tom-biskupic/LabPSU/Firmware/LabPSU/Linearizer.h

/* 
* Linearizer.h
*
* Author: tom
*/

#include <stdint.h>

#ifndef __LINEARIZER_H__
#define __LINEARIZER_H__

/*
The Linearizer is used to linearize the output of a DAC or ADC using a table of measured
values.
To calibrate the output of a DAC we need to adjust the codes used to take into 
account any non-linearities in either the DAC or the system being driven by it.
A simple way of doing this is to store a series of measure points and to linearly
interpolate between those points. The points are a series of float values and 
their corresponding ADC/DAC codes. 

When converting a value to a code or vice versa the class will search for a point
in the table greater than the value in question and then will use the gradient
calculated between that point and the next one to convert to a code/value.
*/
class Linearizer
{
public:
    struct Point
    {		
        uint16_t	code;
        float		value;		
    };
    
	static const int MAX_POINTS = 16;
	
    static const struct Point ZERO_POINT;
    
    Linearizer(uint16_t numPoints=MAX_POINTS,uint16_t min=0,uint16_t max=0xffff);
    
	/*
	Sets the point at the index given. Used to reload the 
	*/
	void setPoint( uint16_t index, const Point& point )
    {
        if ( index >= m_numPoints )
        {
            return;
        }
        
        m_points[index].code = point.code;
        m_points[index].value = point.value;
    }        
	
	/*
	Returns the point at the index provided
	*/
	const Point& getPoint(int index) const
	{
		return m_points[index];
	}
	
	/*
	Sets the min/max values
	*/
	void setMinMax( uint16_t min, uint16_t max);
	
	/*
	Returns the linearizer minimum code
	*/
	const uint16_t getMin() const
	{
		return m_min;
	}

	/*
	Returns the linearizer maximum code
	*/
	const uint16_t getMax() const
	{
		return m_max;
	}

	/*
	Sets the number of points. Used when building a 
	linearizer
	*/
	void setNumPoints(uint16_t numPoints);
	
	const uint16_t getNumPoints() const
	{
		return m_numPoints;
	}
	
    /*
    Calculates the code for the value provided by using
    the table of points provided in the constructor.
    */
    const uint16_t valueToCode(const float value) const;
    
    /*
    Calculates the value given the code provided by using
    the table of points provided in the constructor
    */
    const float codeToValue(const uint16_t code) const;
    
protected:

    /*
    Calculates the code by interpolating using the points provided.
    Uses point1 and point2 to calculate the gradient and then extrapolates
    using this gradient from the basepoint provided.
    */
    uint16_t interpolateCode( 
        const Point&	point1, 
        const Point&	point2, 
        const Point&	basePoint,
        const float		value  ) const;

    /*
    Calculates the code by interpolating using the points provided.
    Uses point1 and point2 to calculate the gradient and then extrapolates
    using this gradient from the basepoint provided.
    */
    float interpolateValue(
        const Point&	point1, 
        const Point&	point2, 
        const Point&	basePoint,
        const uint16_t	code ) const;
        
    Point		m_points[MAX_POINTS];
	uint16_t	m_numPoints;
    uint16_t    m_min;
    uint16_t    m_max;
};

#endif //__LINEARIZER_H__
