tom-biskupic/LabPSU/Firmware/LabPSU/VoltageDACCommand.cpp

/*
* VoltageDACCommand.cpp
*
* Created: 21/07/2015 1:10:31 AM
* Author: tom
*/

#include "VoltageDACCommand.h"
#include "stdio.h"
namespace
{
    const char *VOLTAGE_DAC_COMMAND_NAME = "VDAC";
    const unsigned int MIN_RANGE = 0;
    const unsigned int MAX_RANGE = 0xffff;
}

VoltageDACCommand::VoltageDACCommand() : Command(VOLTAGE_DAC_COMMAND_NAME)
{
    
}

void VoltageDACCommand::handleSetCommand( const char *params, LabPSU *labPSU )
{
    unsigned int count;
    if ( parseHexParam(count,params) )
    {
        if ( withinRange(MIN_RANGE,MAX_RANGE,count))
        {
            labPSU->setVoltageDACCount(count);
            printFloat(labPSU->getOutputVoltageLimit());
        }
    }
}

void VoltageDACCommand::handleGetCommand(LabPSU *labPSU) const
{
    printFloat(labPSU->getOutputVoltageLimit());
}
